JanSolo99/digital-radio-alarm/docs/img/alt-pebble-cutaway.png

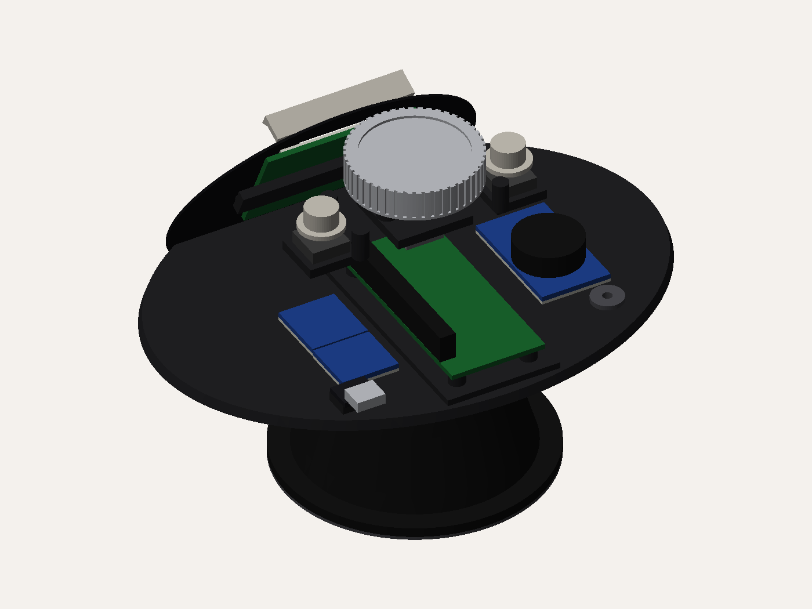
docs/img/alt-pebble-cutaway.png
