JanSolo99/digital-radio-alarm/docs/img/alt-pebble-front-three-quarter.png

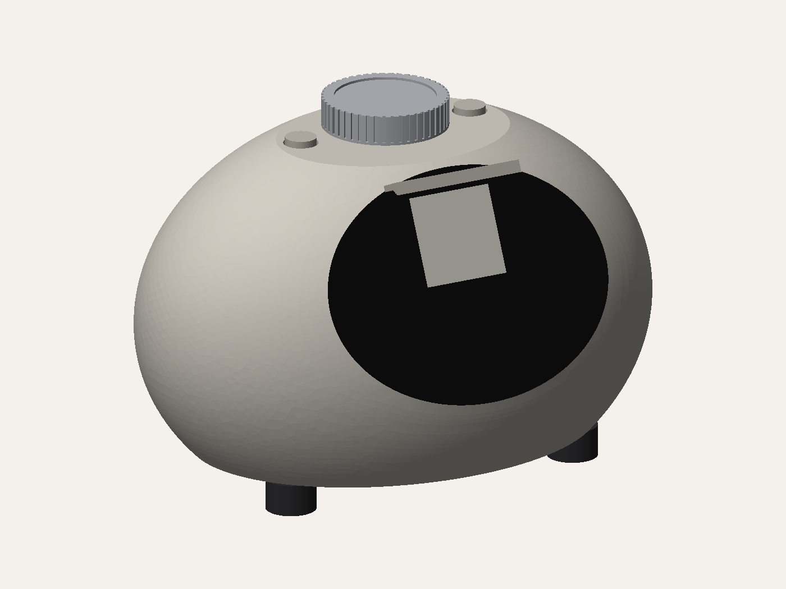
docs/img/alt-pebble-front-three-quarter.png
