JanSolo99/digital-radio-alarm/docs/img/alt-pebble-underside.png

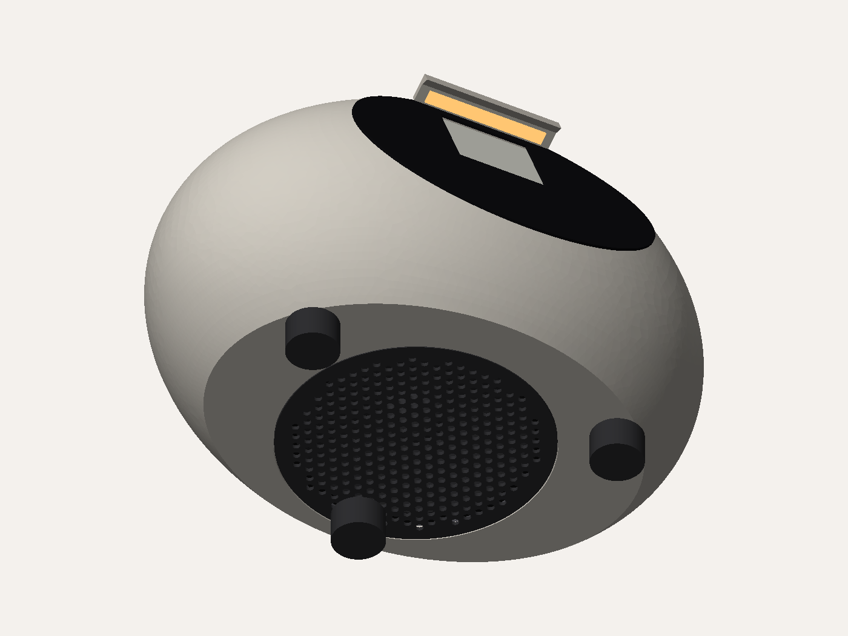
docs/img/alt-pebble-underside.png
