JanSolo99/digital-radio-alarm/docs/img/alt-sunrise-cutaway.png

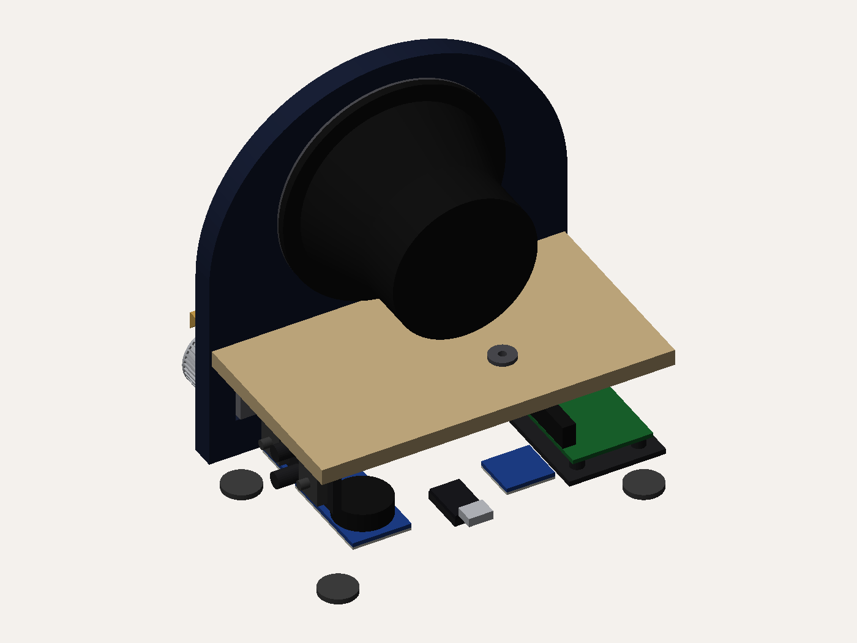
docs/img/alt-sunrise-cutaway.png
