JanSolo99/digital-radio-alarm/docs/img/alt-sunrise-front-three-quarter.png

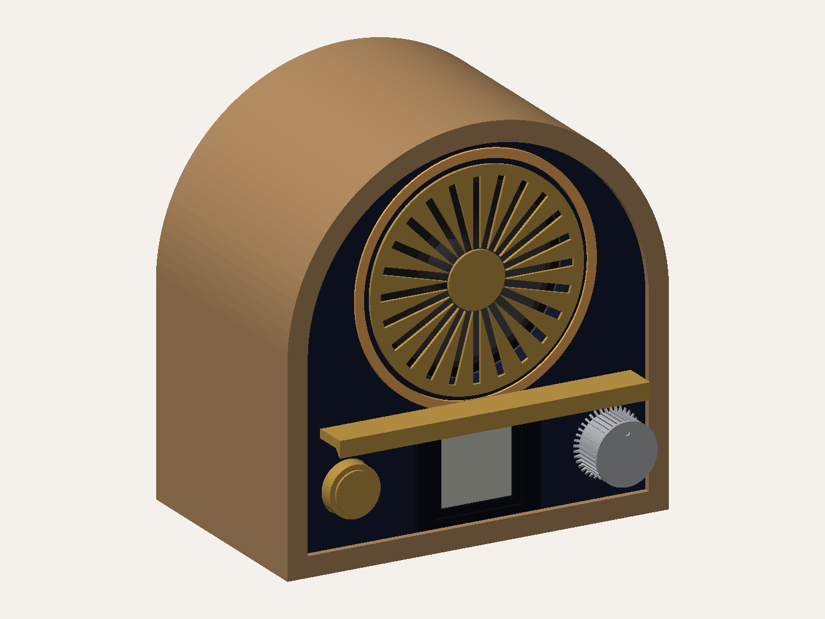
docs/img/alt-sunrise-front-three-quarter.png
