JanSolo99/digital-radio-alarm/docs/img/alt-sunrise-front.png

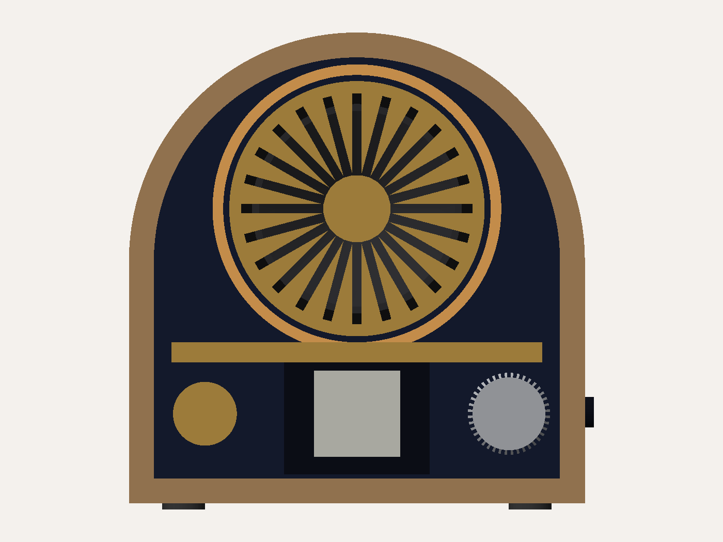
docs/img/alt-sunrise-front.png
