JanSolo99/digital-radio-alarm/docs/img/alt-sunrise-rear-three-quarter.png

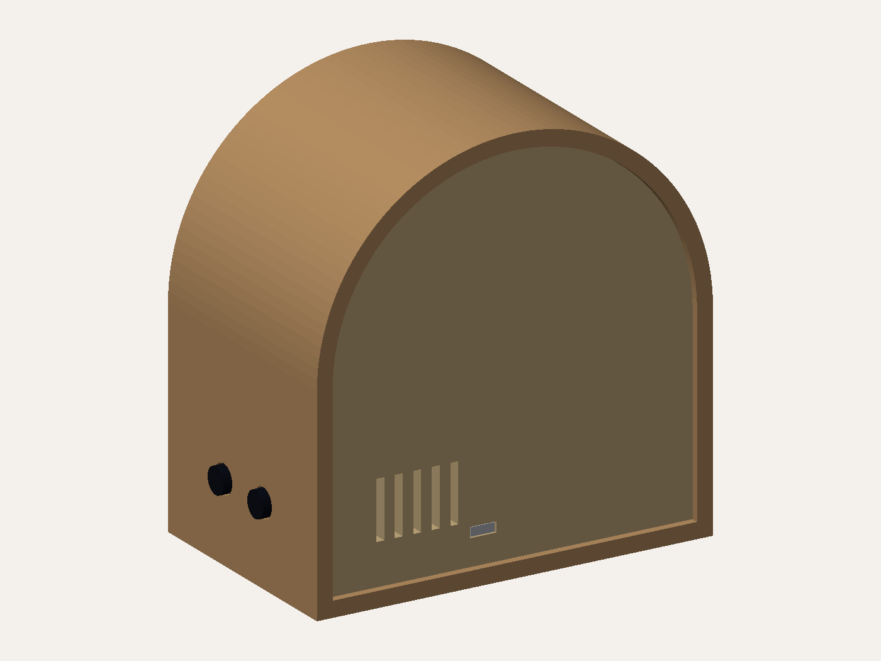
docs/img/alt-sunrise-rear-three-quarter.png
