JanSolo99/digital-radio-alarm/docs/img/radio-cutaway.png

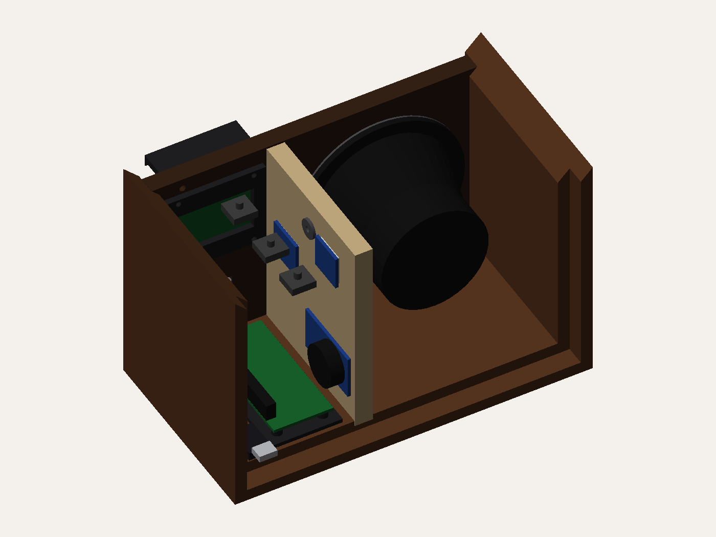
docs/img/radio-cutaway.png
