JanSolo99/digital-radio-alarm/docs/img/radio-exploded.png

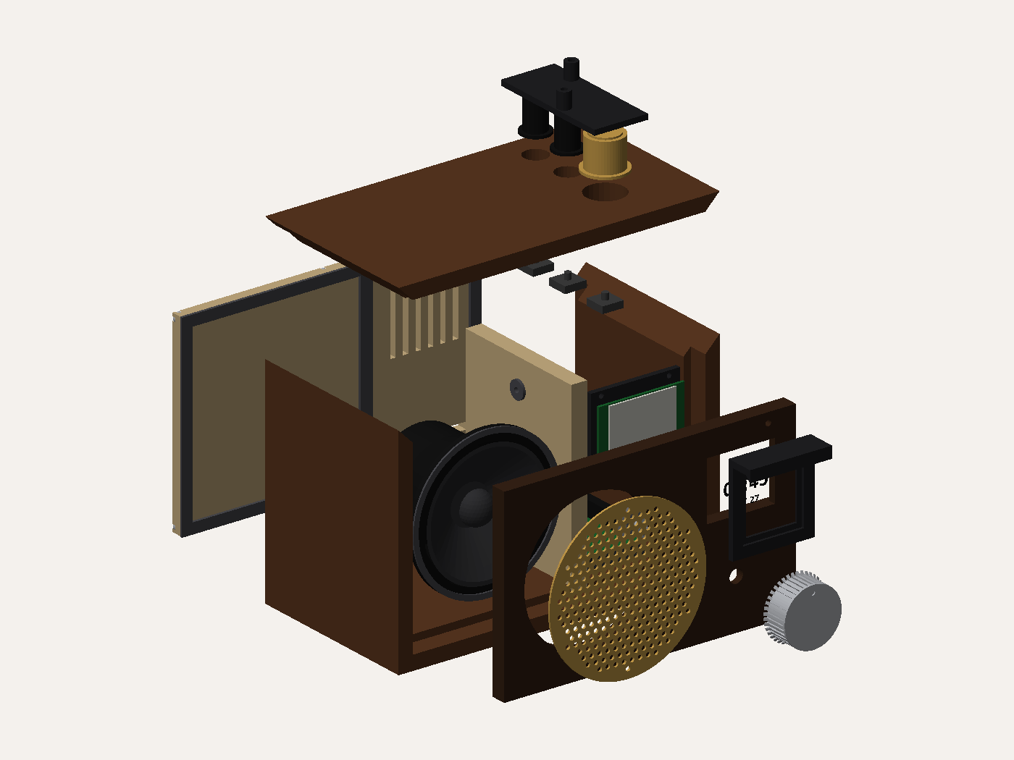
docs/img/radio-exploded.png
