JanSolo99/digital-radio-alarm/docs/img/radio-front-three-quarter.png

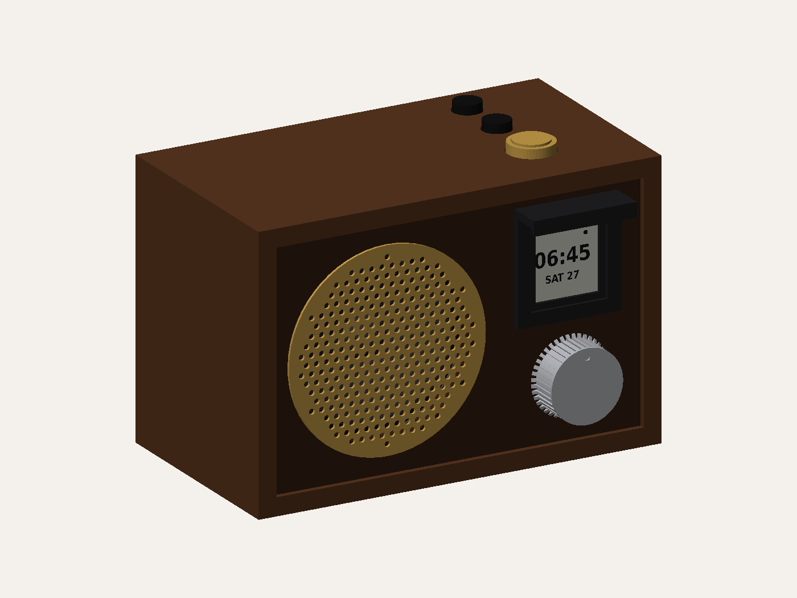
docs/img/radio-front-three-quarter.png
