JanSolo99/digital-radio-alarm/docs/img/radio-front.png

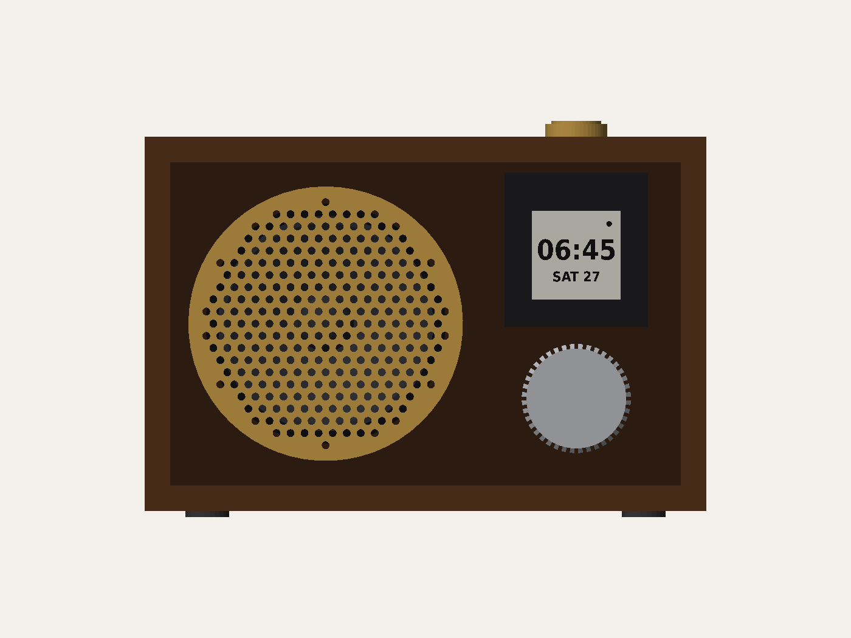
docs/img/radio-front.png
