JanSolo99/digital-radio-alarm/docs/img/radio-rear-open.png

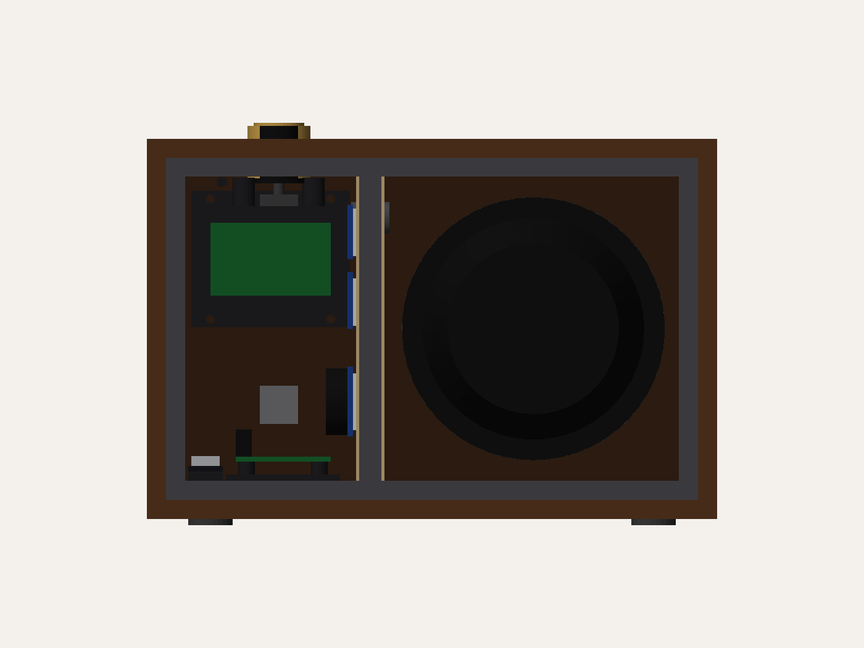
docs/img/radio-rear-open.png
