JanSolo99/digital-radio-alarm/cad/stl/Carcass_Bottom.stl

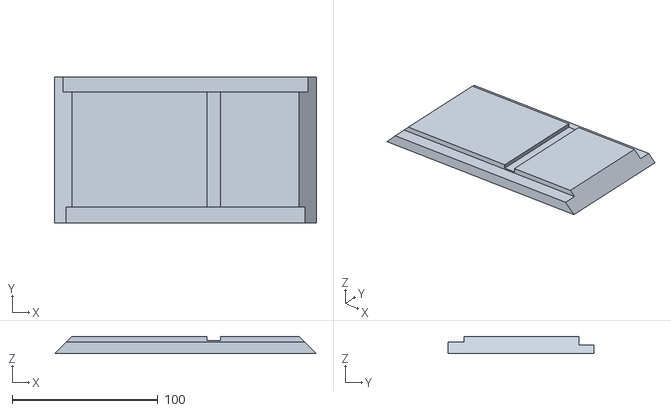
[picture p33: CAD file, 2026-09-27]
cad/stl/Carcass_Bottom.stl
180.0 x 100.0 x 12.0
