JanSolo99/digital-radio-alarm/cad/stl/USBC_Saddle.stl

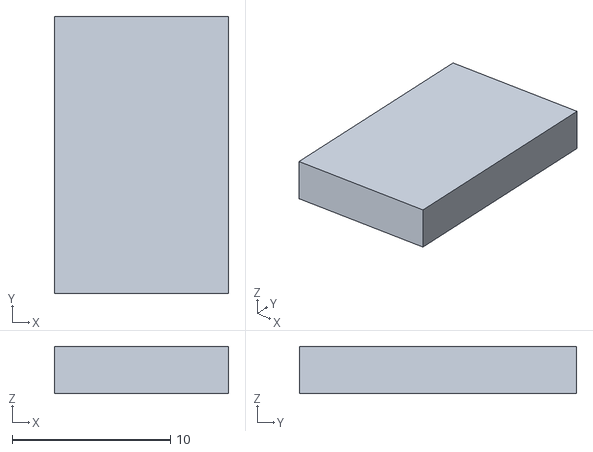
[picture p34: CAD file, 2026-09-27]
cad/stl/USBC_Saddle.stl
11.0 x 17.5 x 3.00
