JanSolo99/digital-radio-alarm/cad/stl/Display_Clamp.stl

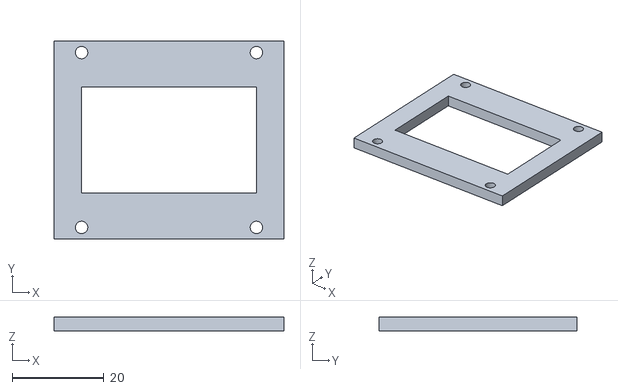
[picture p35: CAD file, 2026-09-27]
cad/stl/Display_Clamp.stl
50.0 x 43.0 x 3.00
